rfrht/SignalSurge/others/cap-kit.jpg

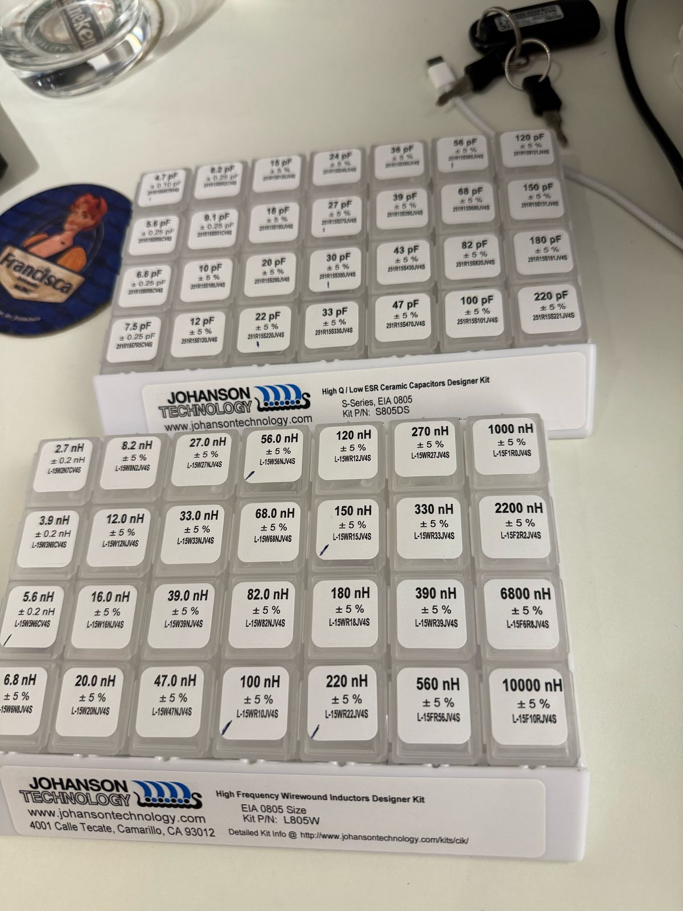
others/cap-kit.jpg
