rfrht/SignalSurge/others/encased-miniature-filter.jpg

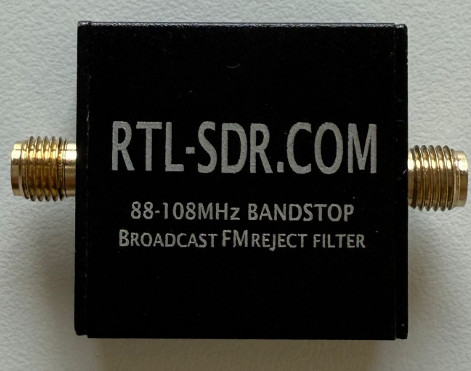
others/encased-miniature-filter.jpg
