rfrht/SignalSurge/others/miniature-filter-board.jpg

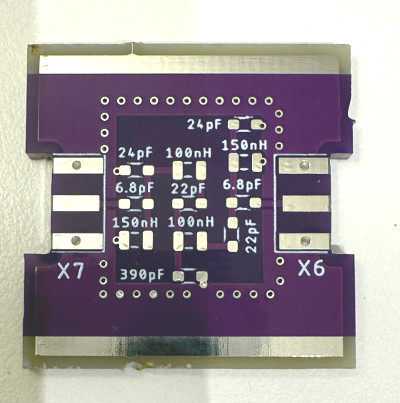
others/miniature-filter-board.jpg
