rfrht/SignalSurge/others/miniature-filter.jpg

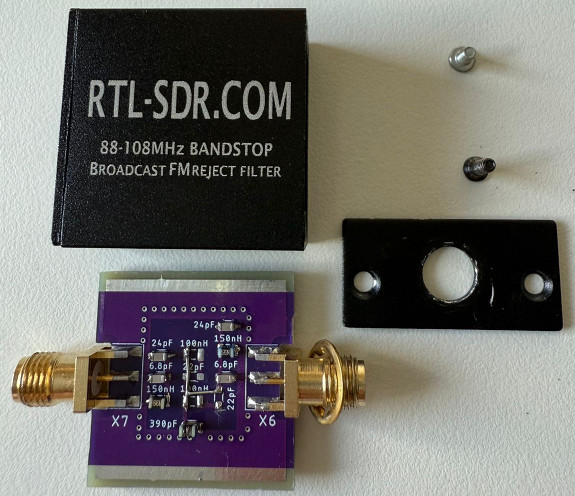
others/miniature-filter.jpg
