rfrht/SignalSurge/others/ss-board-finished.jpg

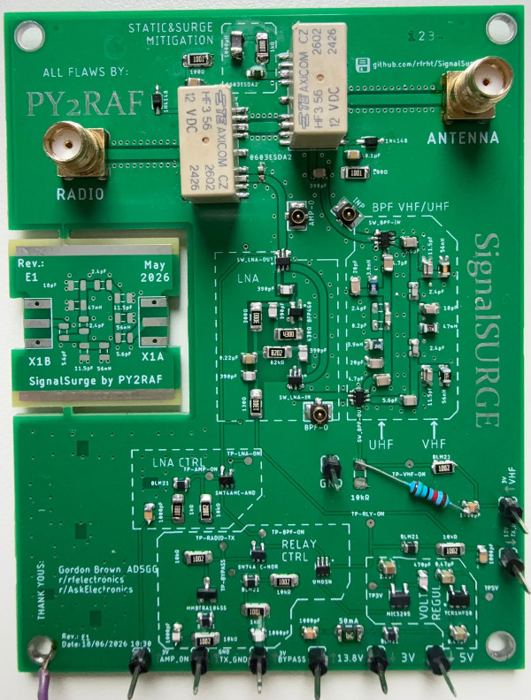
others/ss-board-finished.jpg
