rfrht/SignalSurge/others/test/1-uhf.png

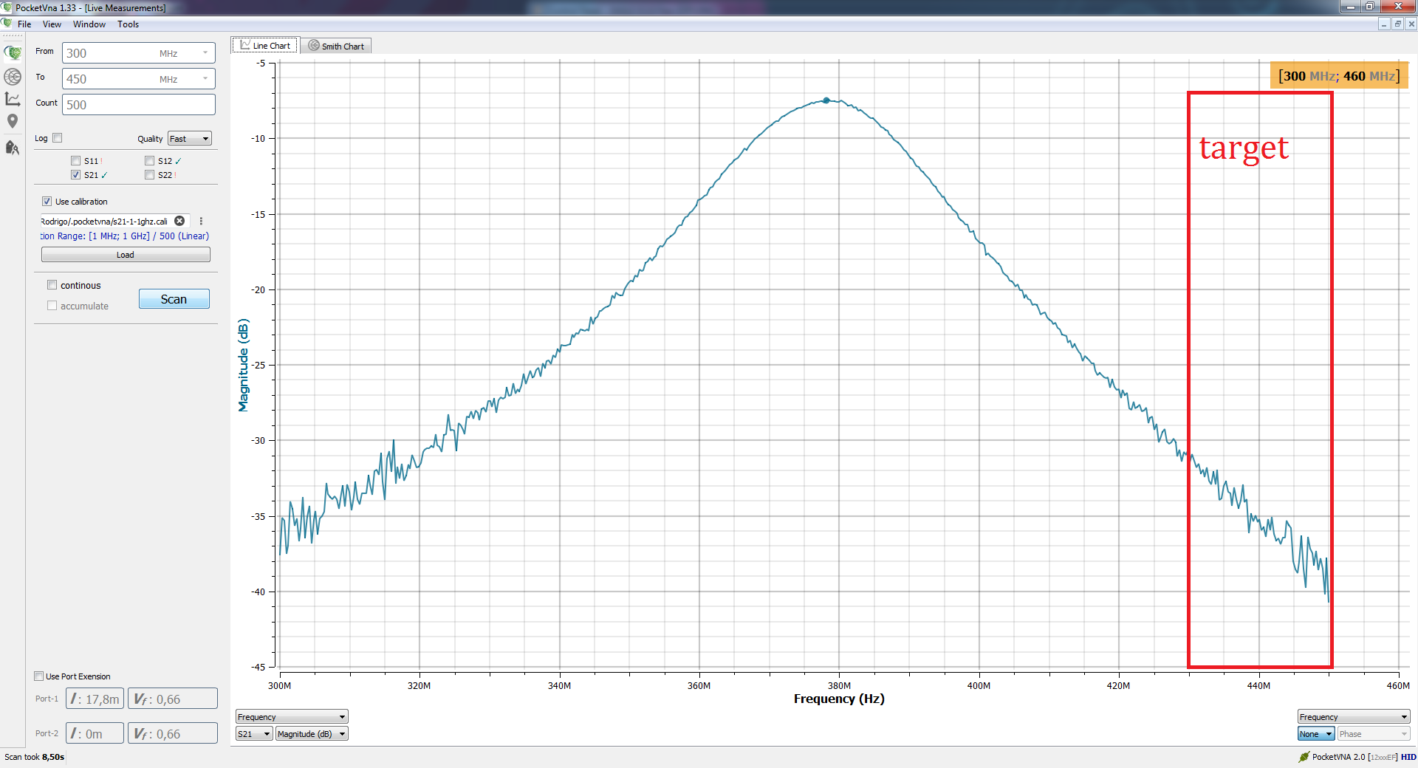
others/test/1-uhf.png
