rfrht/SignalSurge/others/test/bpf-2m-2026-02-22-144-148.png

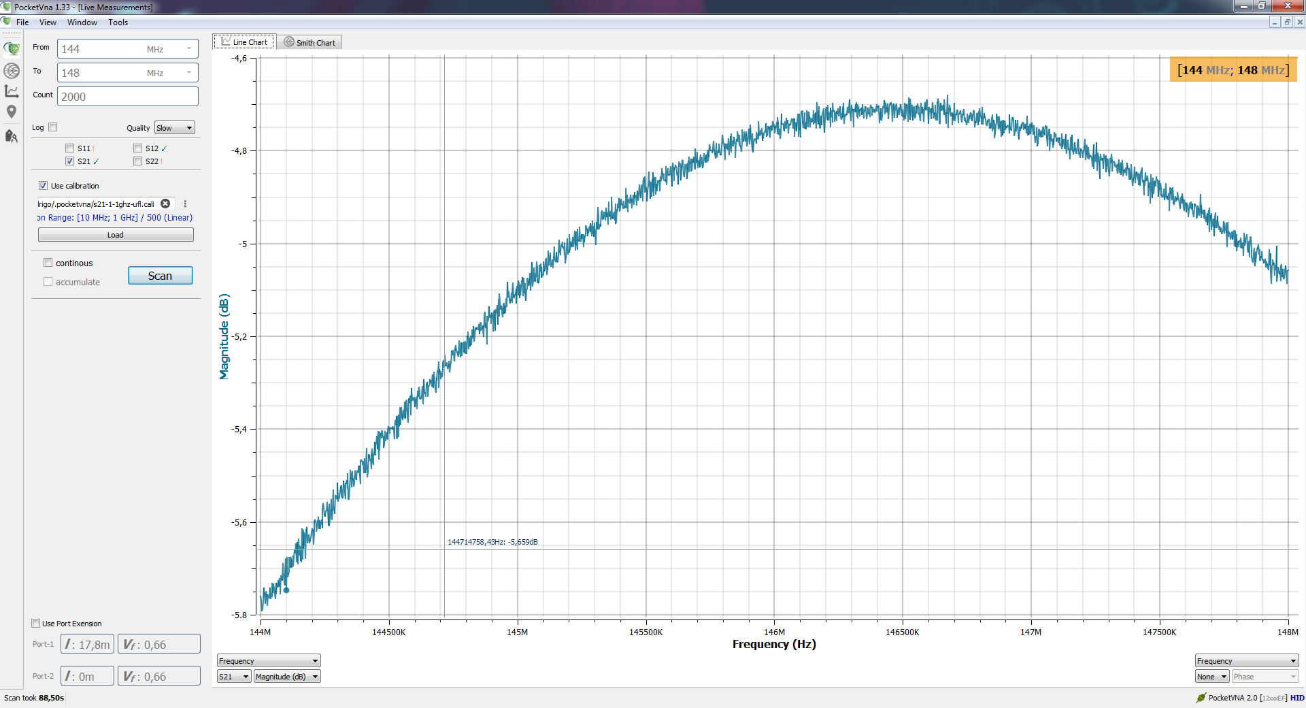
others/test/bpf-2m-2026-02-22-144-148.png
