rfrht/SignalSurge/others/test/bpf-rtlsdr-2025-03-16-80-120.png

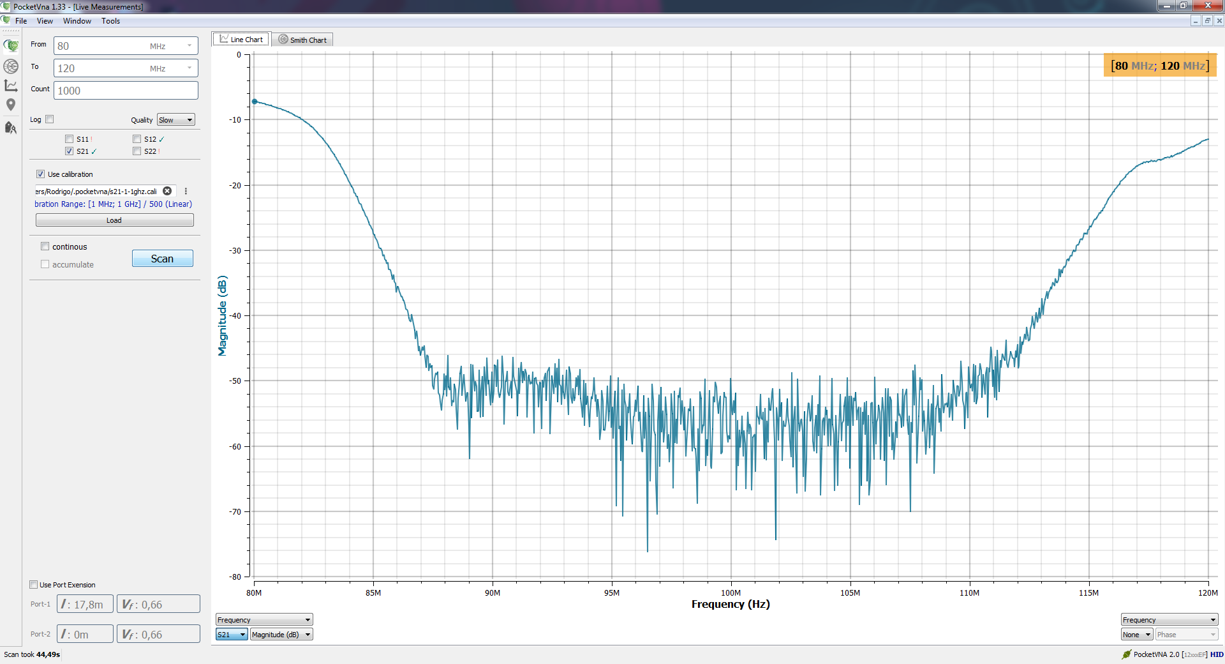
others/test/bpf-rtlsdr-2025-03-16-80-120.png
