rfrht/SignalSurge/others/test/bpf-vhf-gemini-2025-12-25-10-300.png

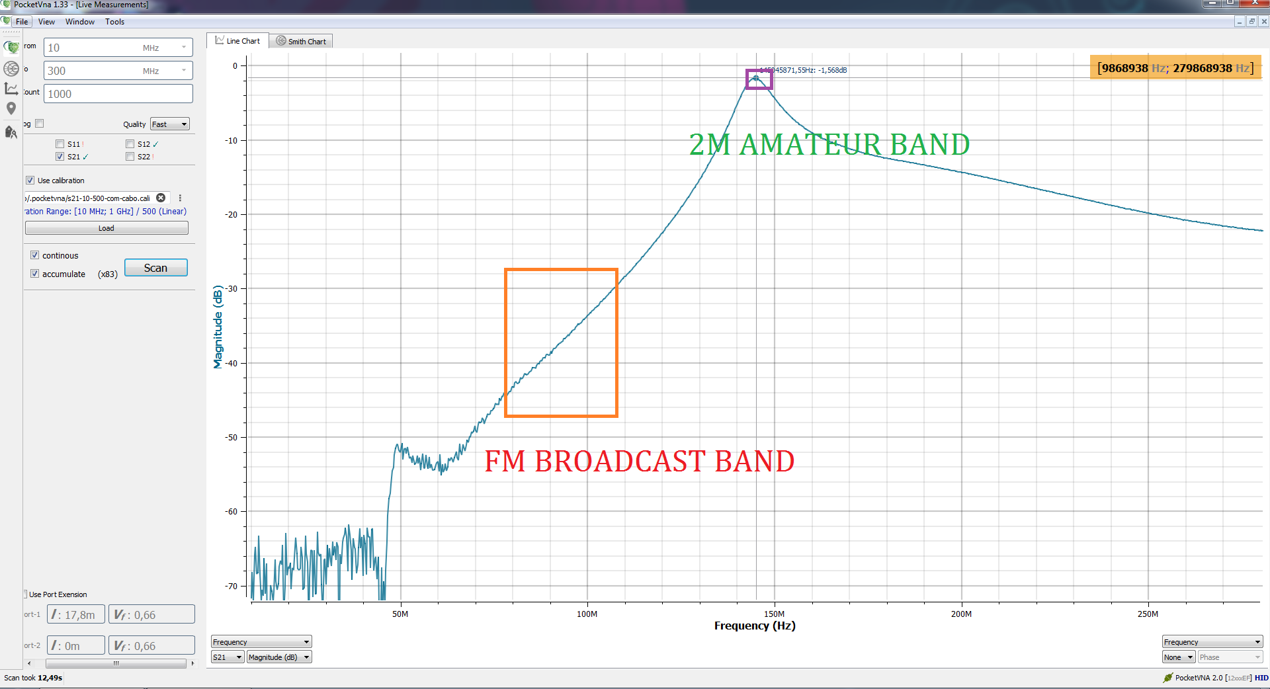
others/test/bpf-vhf-gemini-2025-12-25-10-300.png
