rfrht/SignalSurge/others/test/bpf-vhf-gemini-2025-12-25-76-108.png

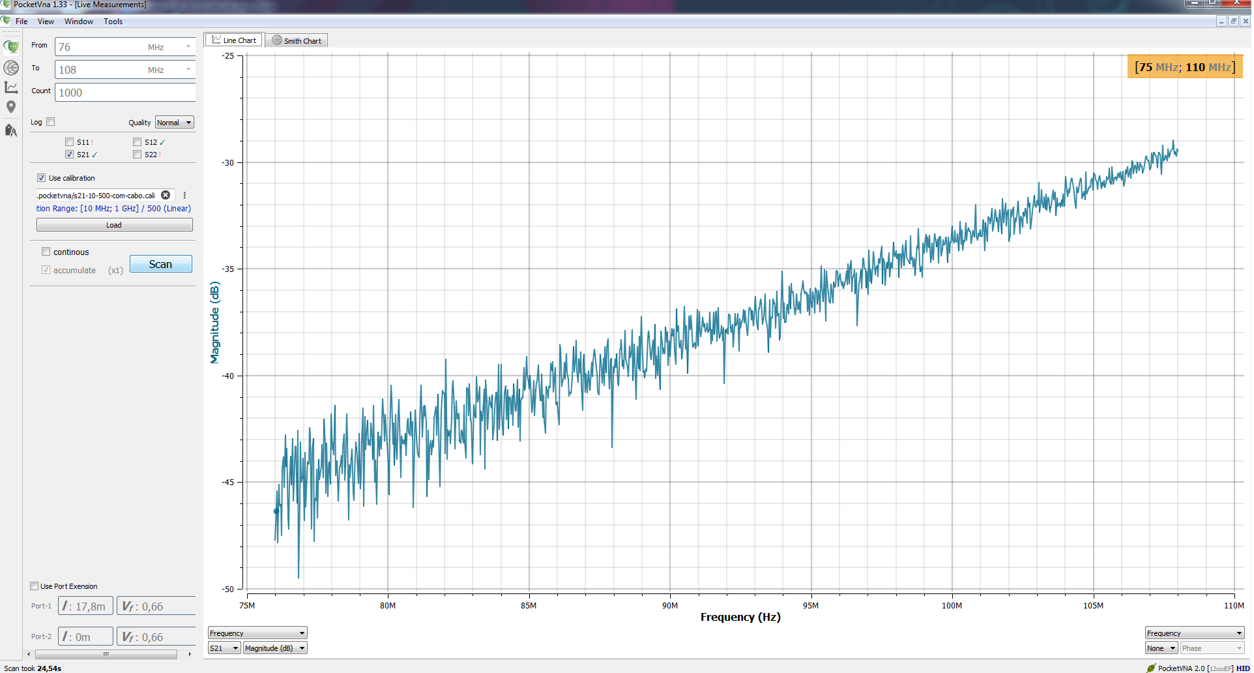
others/test/bpf-vhf-gemini-2025-12-25-76-108.png
