rfrht/SignalSurge/others/test/bpf-vhf-gemini-2025-12-25-144-148.png

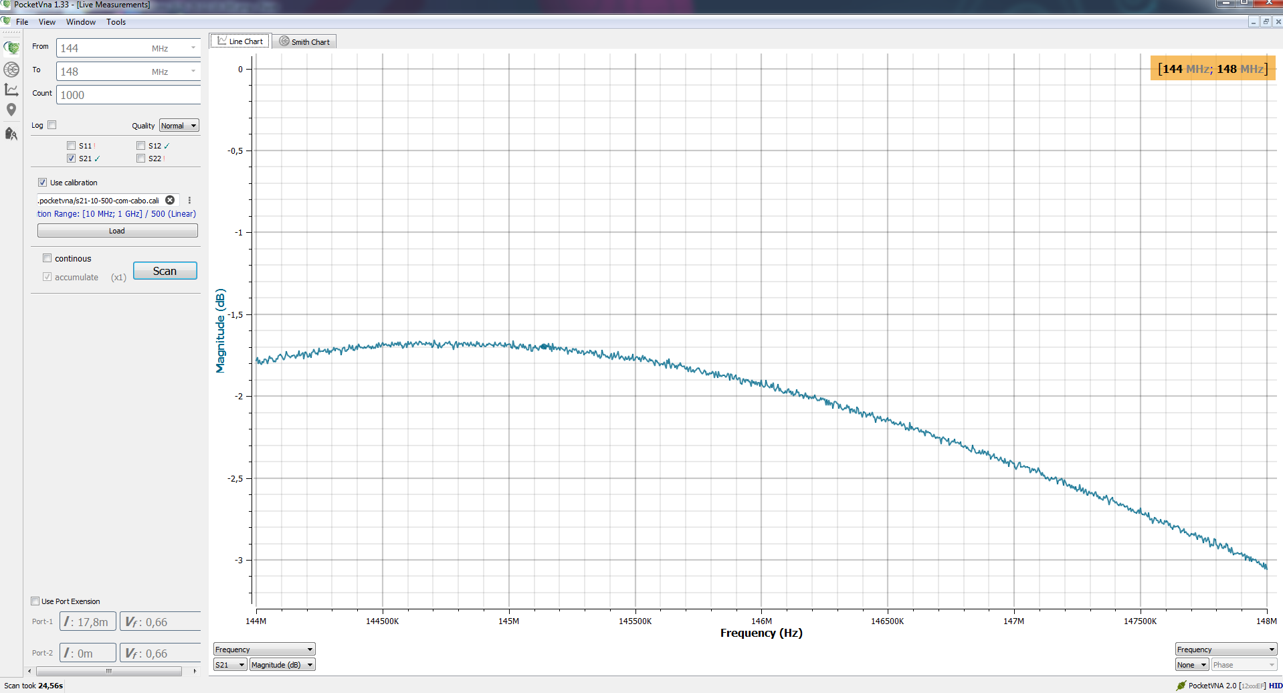
others/test/bpf-vhf-gemini-2025-12-25-144-148.png
