rfrht/SignalSurge/others/test/bpf-vhf-tuned-2025-03-16-1-1000.png

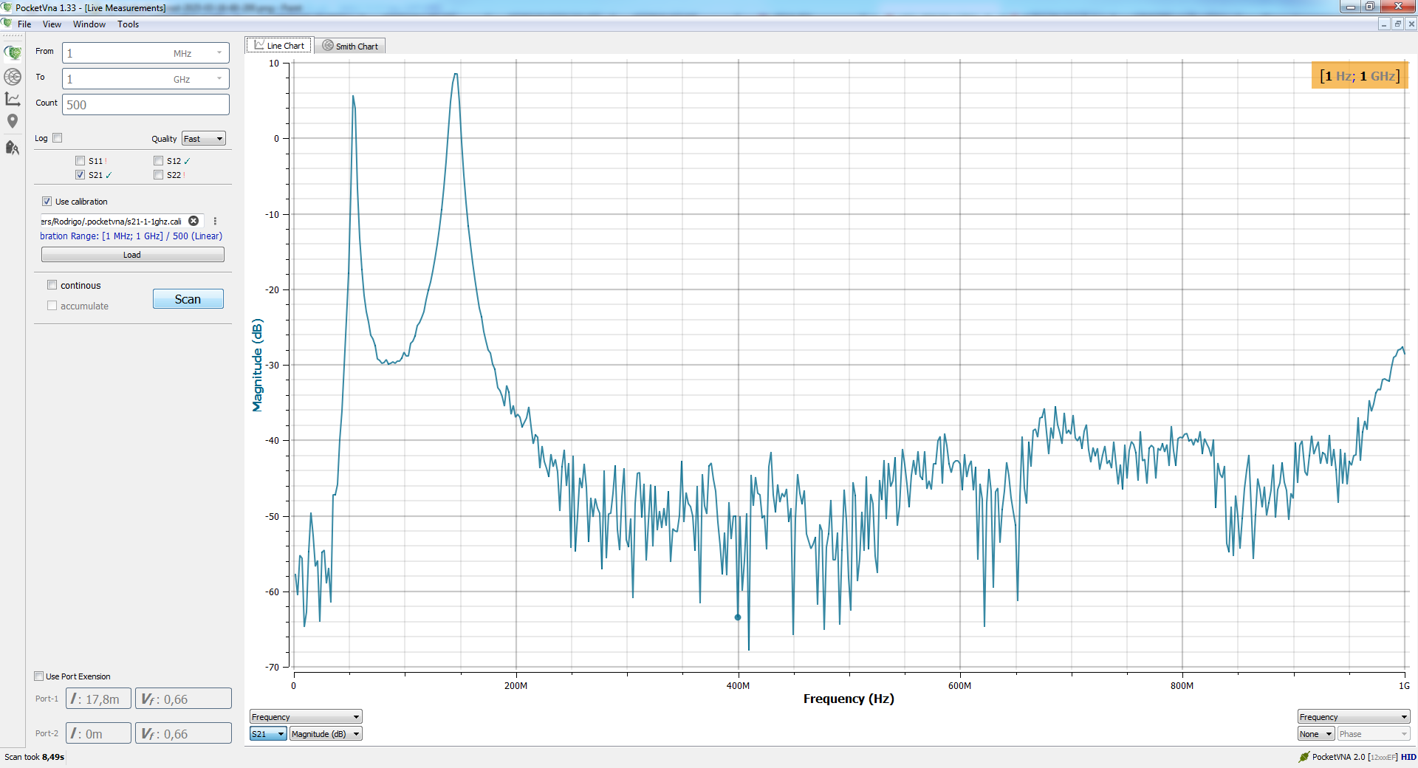
others/test/bpf-vhf-tuned-2025-03-16-1-1000.png
