rfrht/SignalSurge/others/test/bpf-vhf-tuned-2025-03-16.png

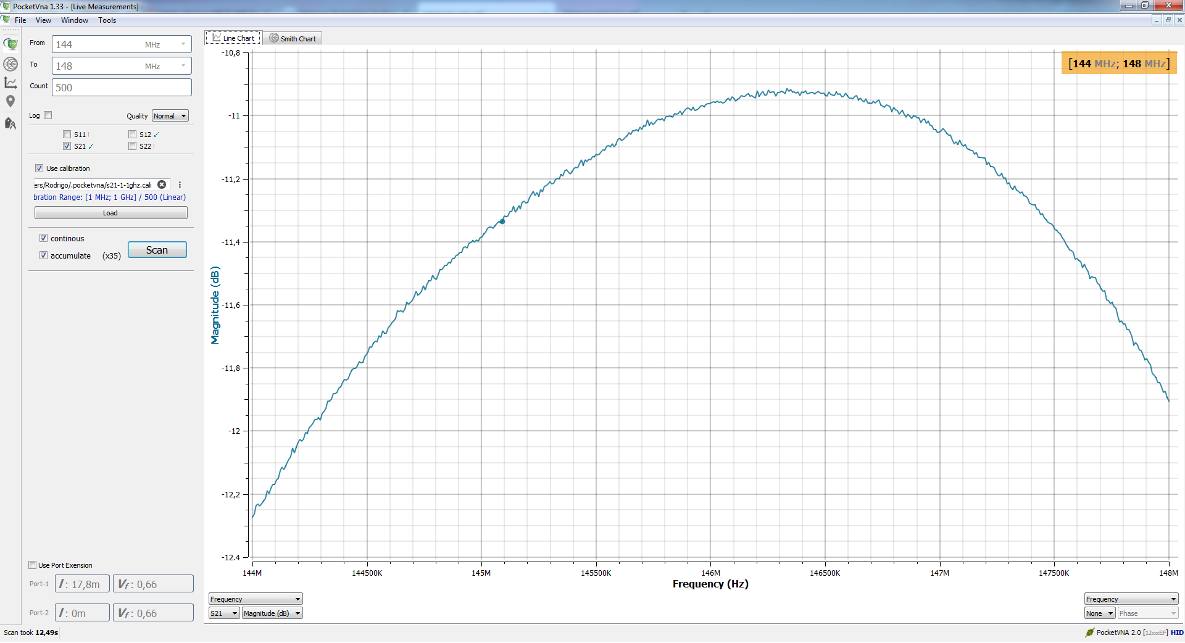
others/test/bpf-vhf-tuned-2025-03-16.png
