rfrht/SignalSurge/others/test/e2e-2m-amp-off.png

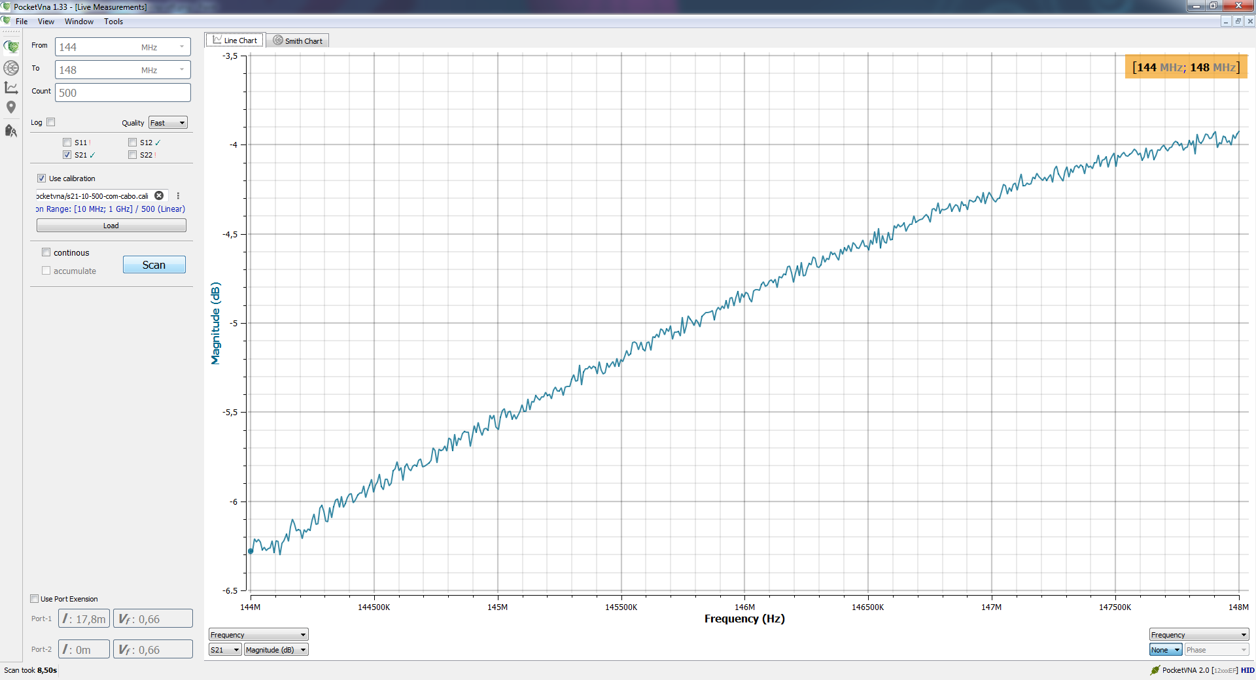
others/test/e2e-2m-amp-off.png
