rfrht/SignalSurge/others/test/e2e-2m-amp-on.png

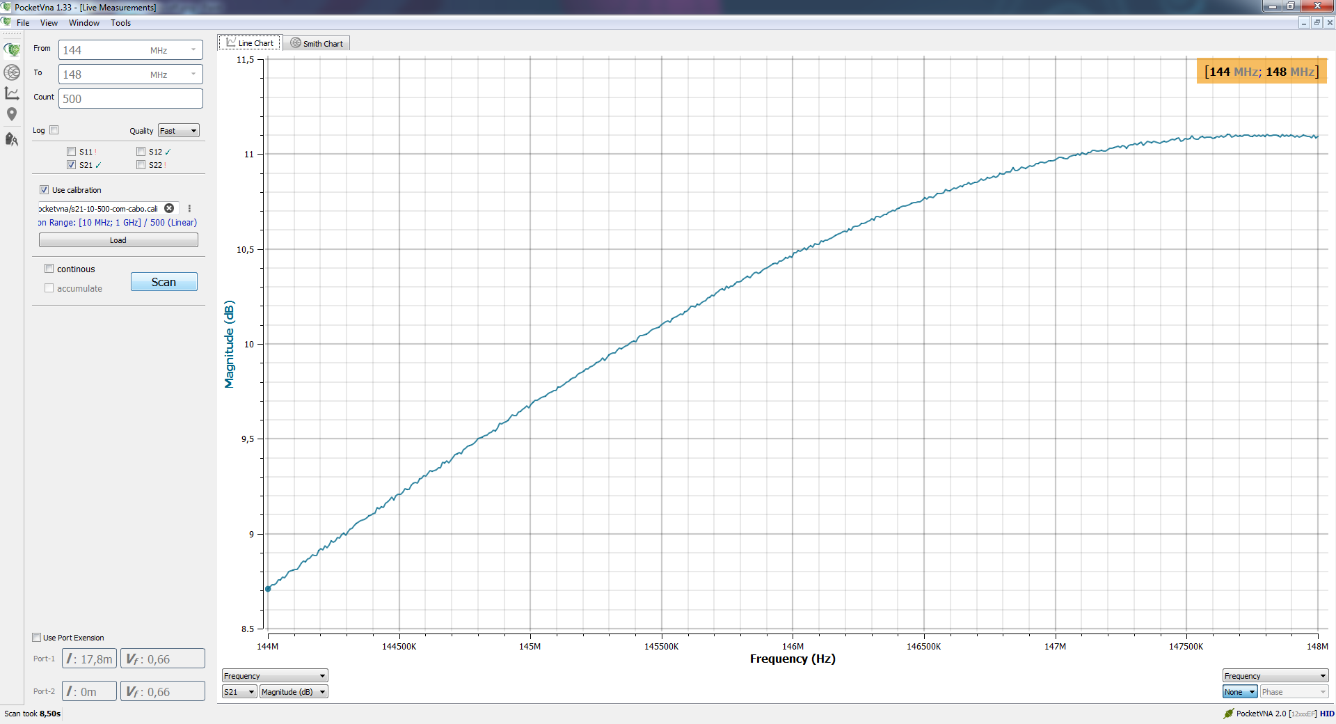
others/test/e2e-2m-amp-on.png
