rfrht/SignalSurge/others/test/e2e-70cm-amp-off.png

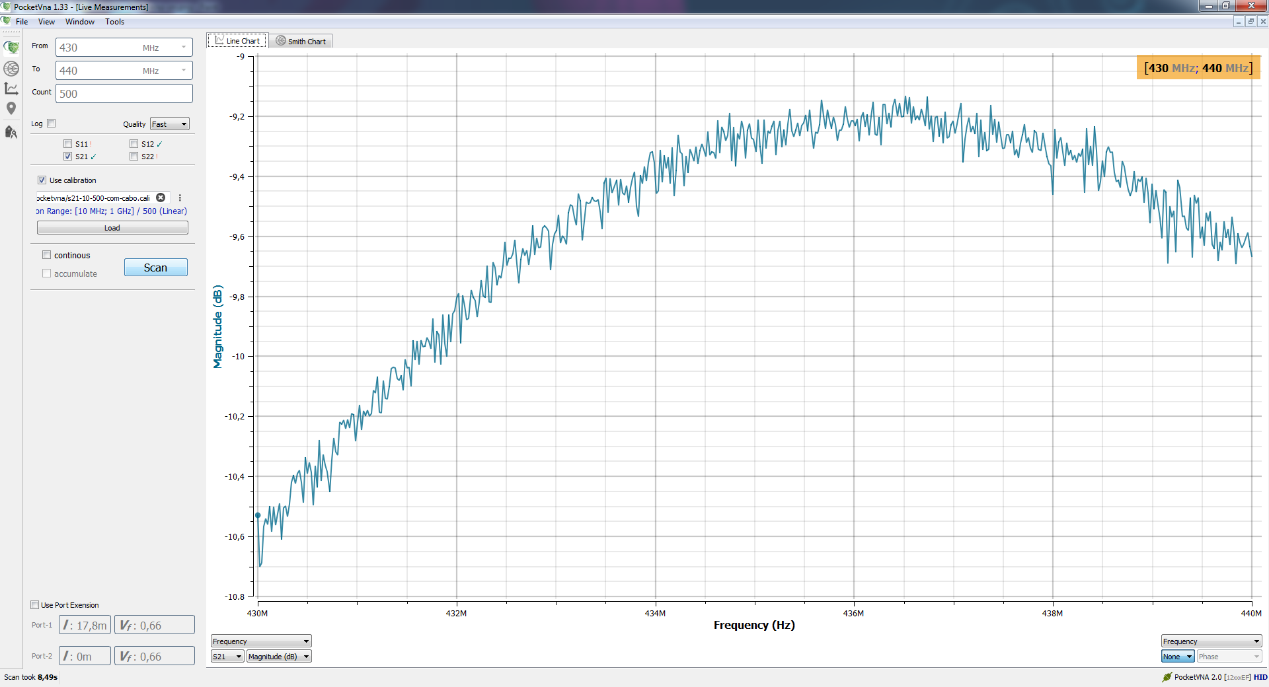
others/test/e2e-70cm-amp-off.png
