rfrht/SignalSurge/others/test/e2e-70cm-amp-on.png

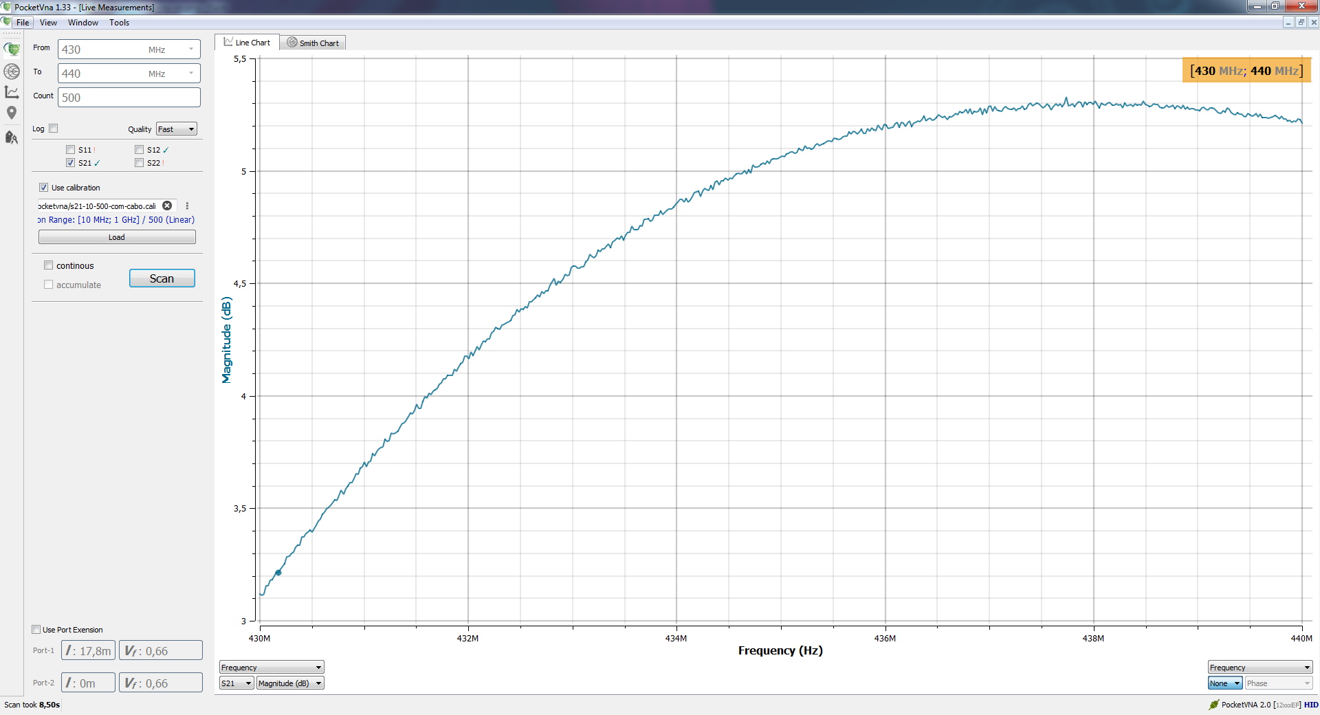
others/test/e2e-70cm-amp-on.png
