rfrht/SignalSurge/others/test/vswr-60-500.png

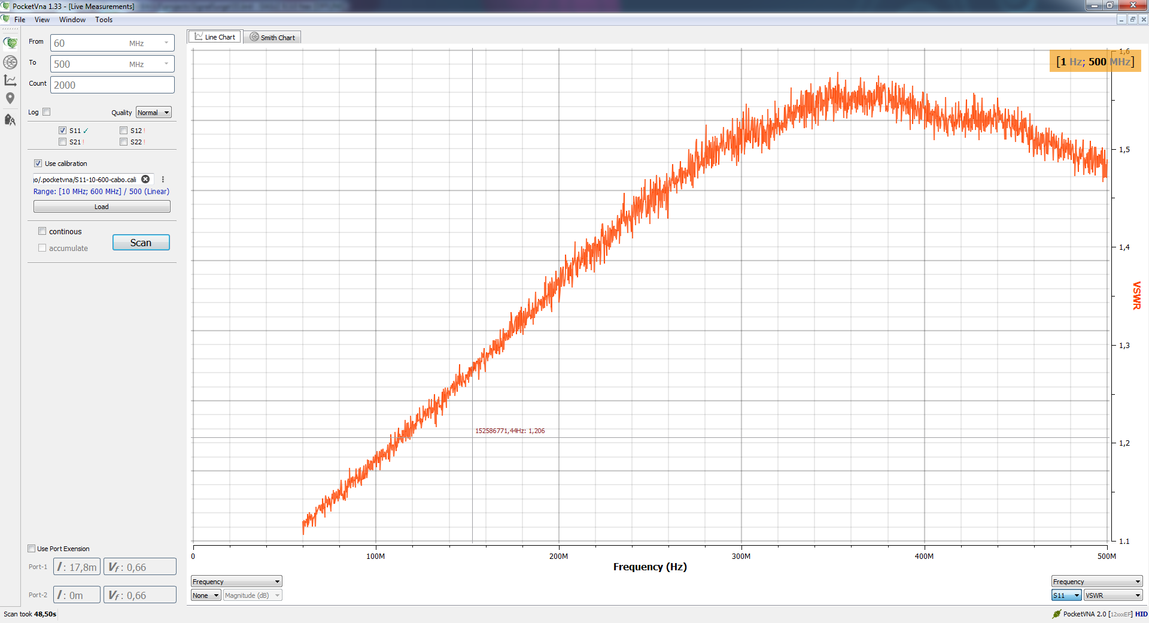
others/test/vswr-60-500.png
